xunker/simple_sl2.1a_usb_hub/images/pcb.jpg

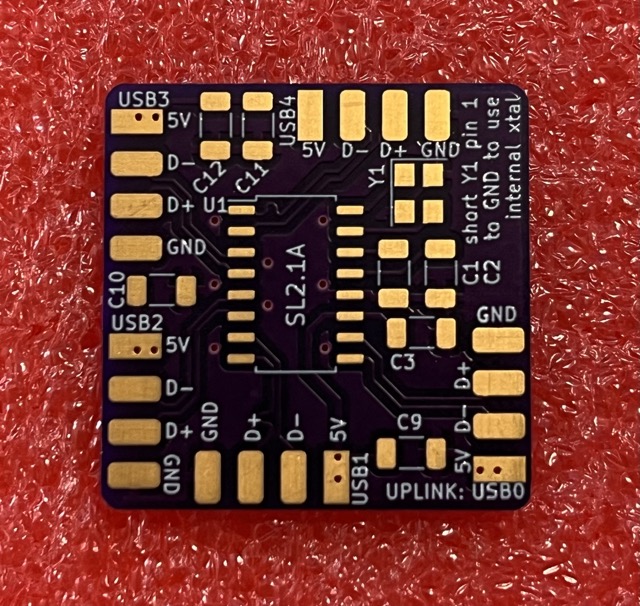
images/pcb.jpg
